ucfnnbx/occupancy-sensing/mobile application/occupancy/assets/images/detail_lounge1_2.jpg

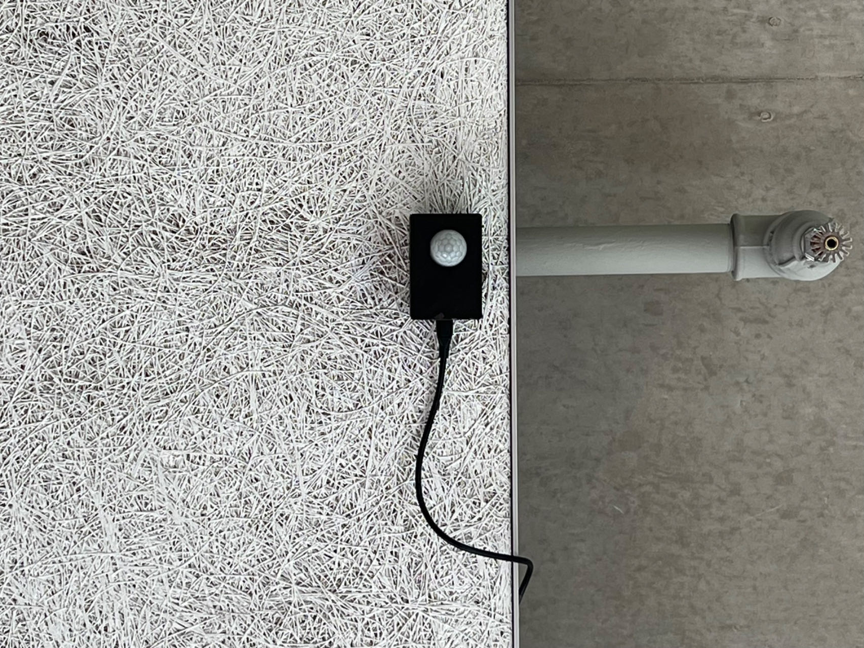
mobile application/occupancy/assets/images/detail_lounge1_2.jpg
