ucfnnbx/occupancy-sensing/mobile application/occupancy/assets/images/detail_lounge4_1.png

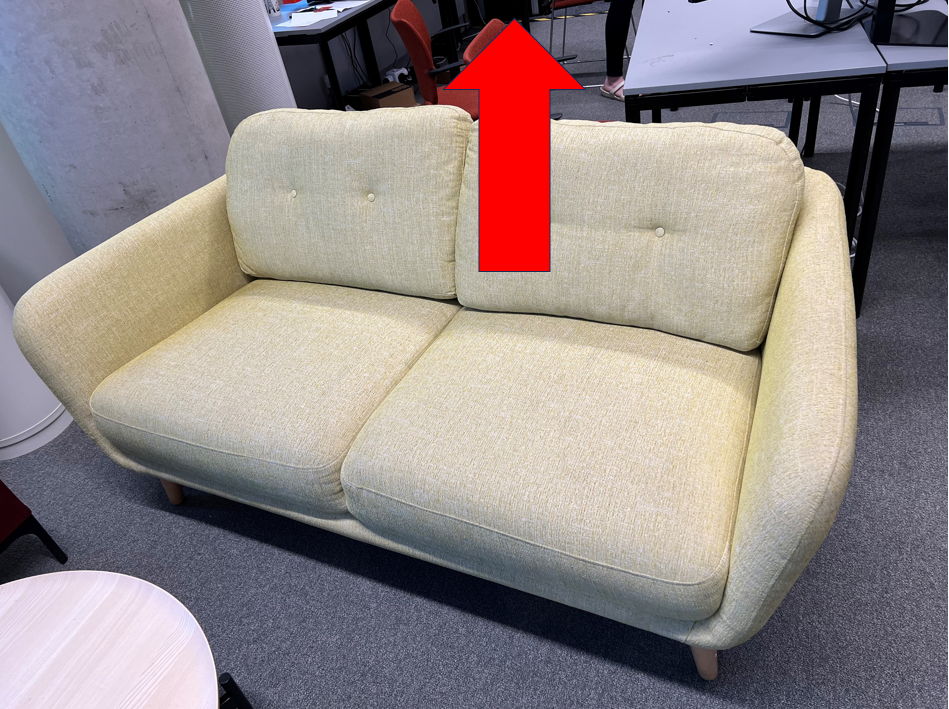
mobile application/occupancy/assets/images/detail_lounge4_1.png
