ucfnnbx/occupancy-sensing/mobile application/occupancy/assets/images/detail_telephone_1.png

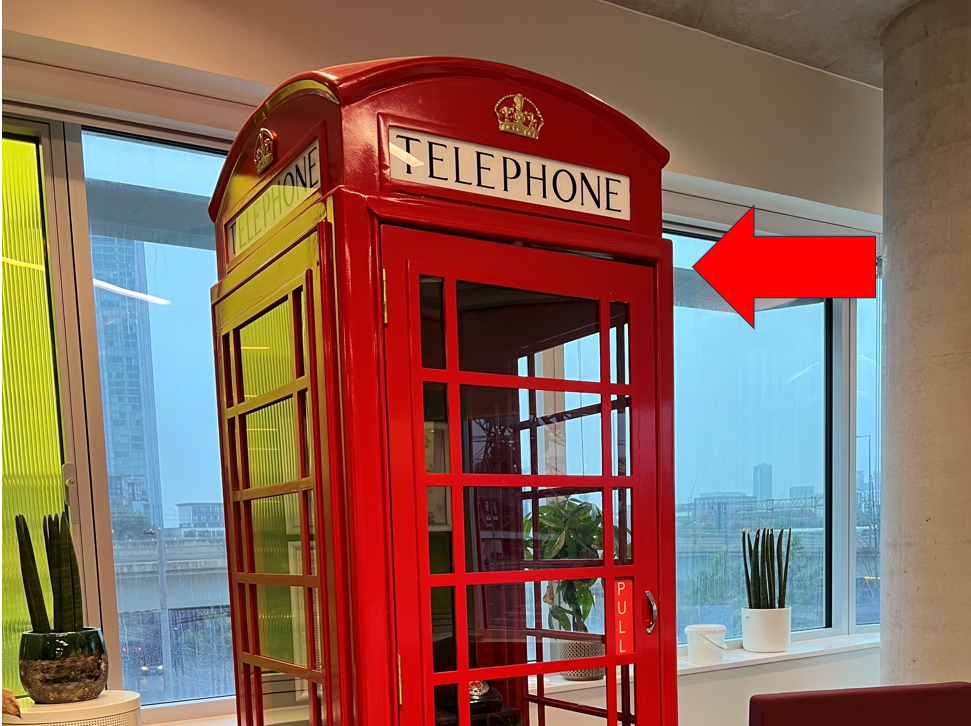
mobile application/occupancy/assets/images/detail_telephone_1.png
