ucfnnbx/occupancy-sensing/readme_images/mobile_app.png

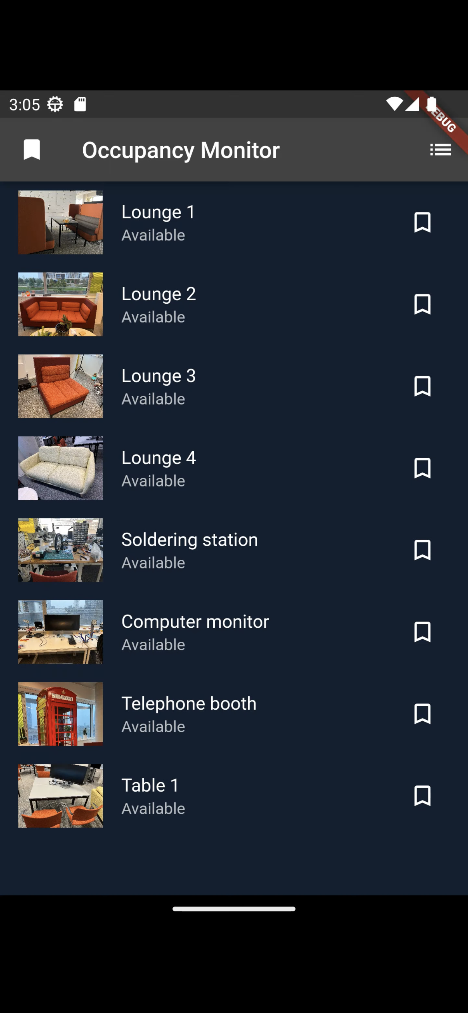
readme_images/mobile_app.png
