ucfnnbx/occupancy-sensing/mobile application/occupancy/assets/images/detail_soldering_1.png

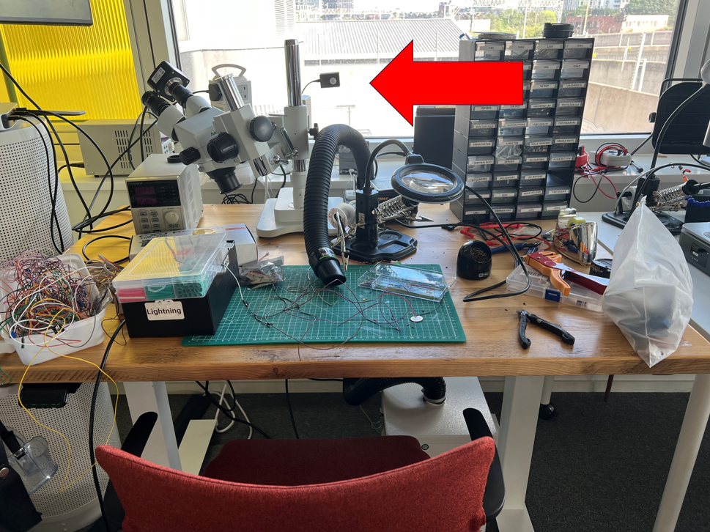
mobile application/occupancy/assets/images/detail_soldering_1.png
